OpenModbus/OM-64DO/kicad/OM-64DO.kicad_sch

## KiCad design kicad/OM-64DO.kicad_sch (2026-03-12)

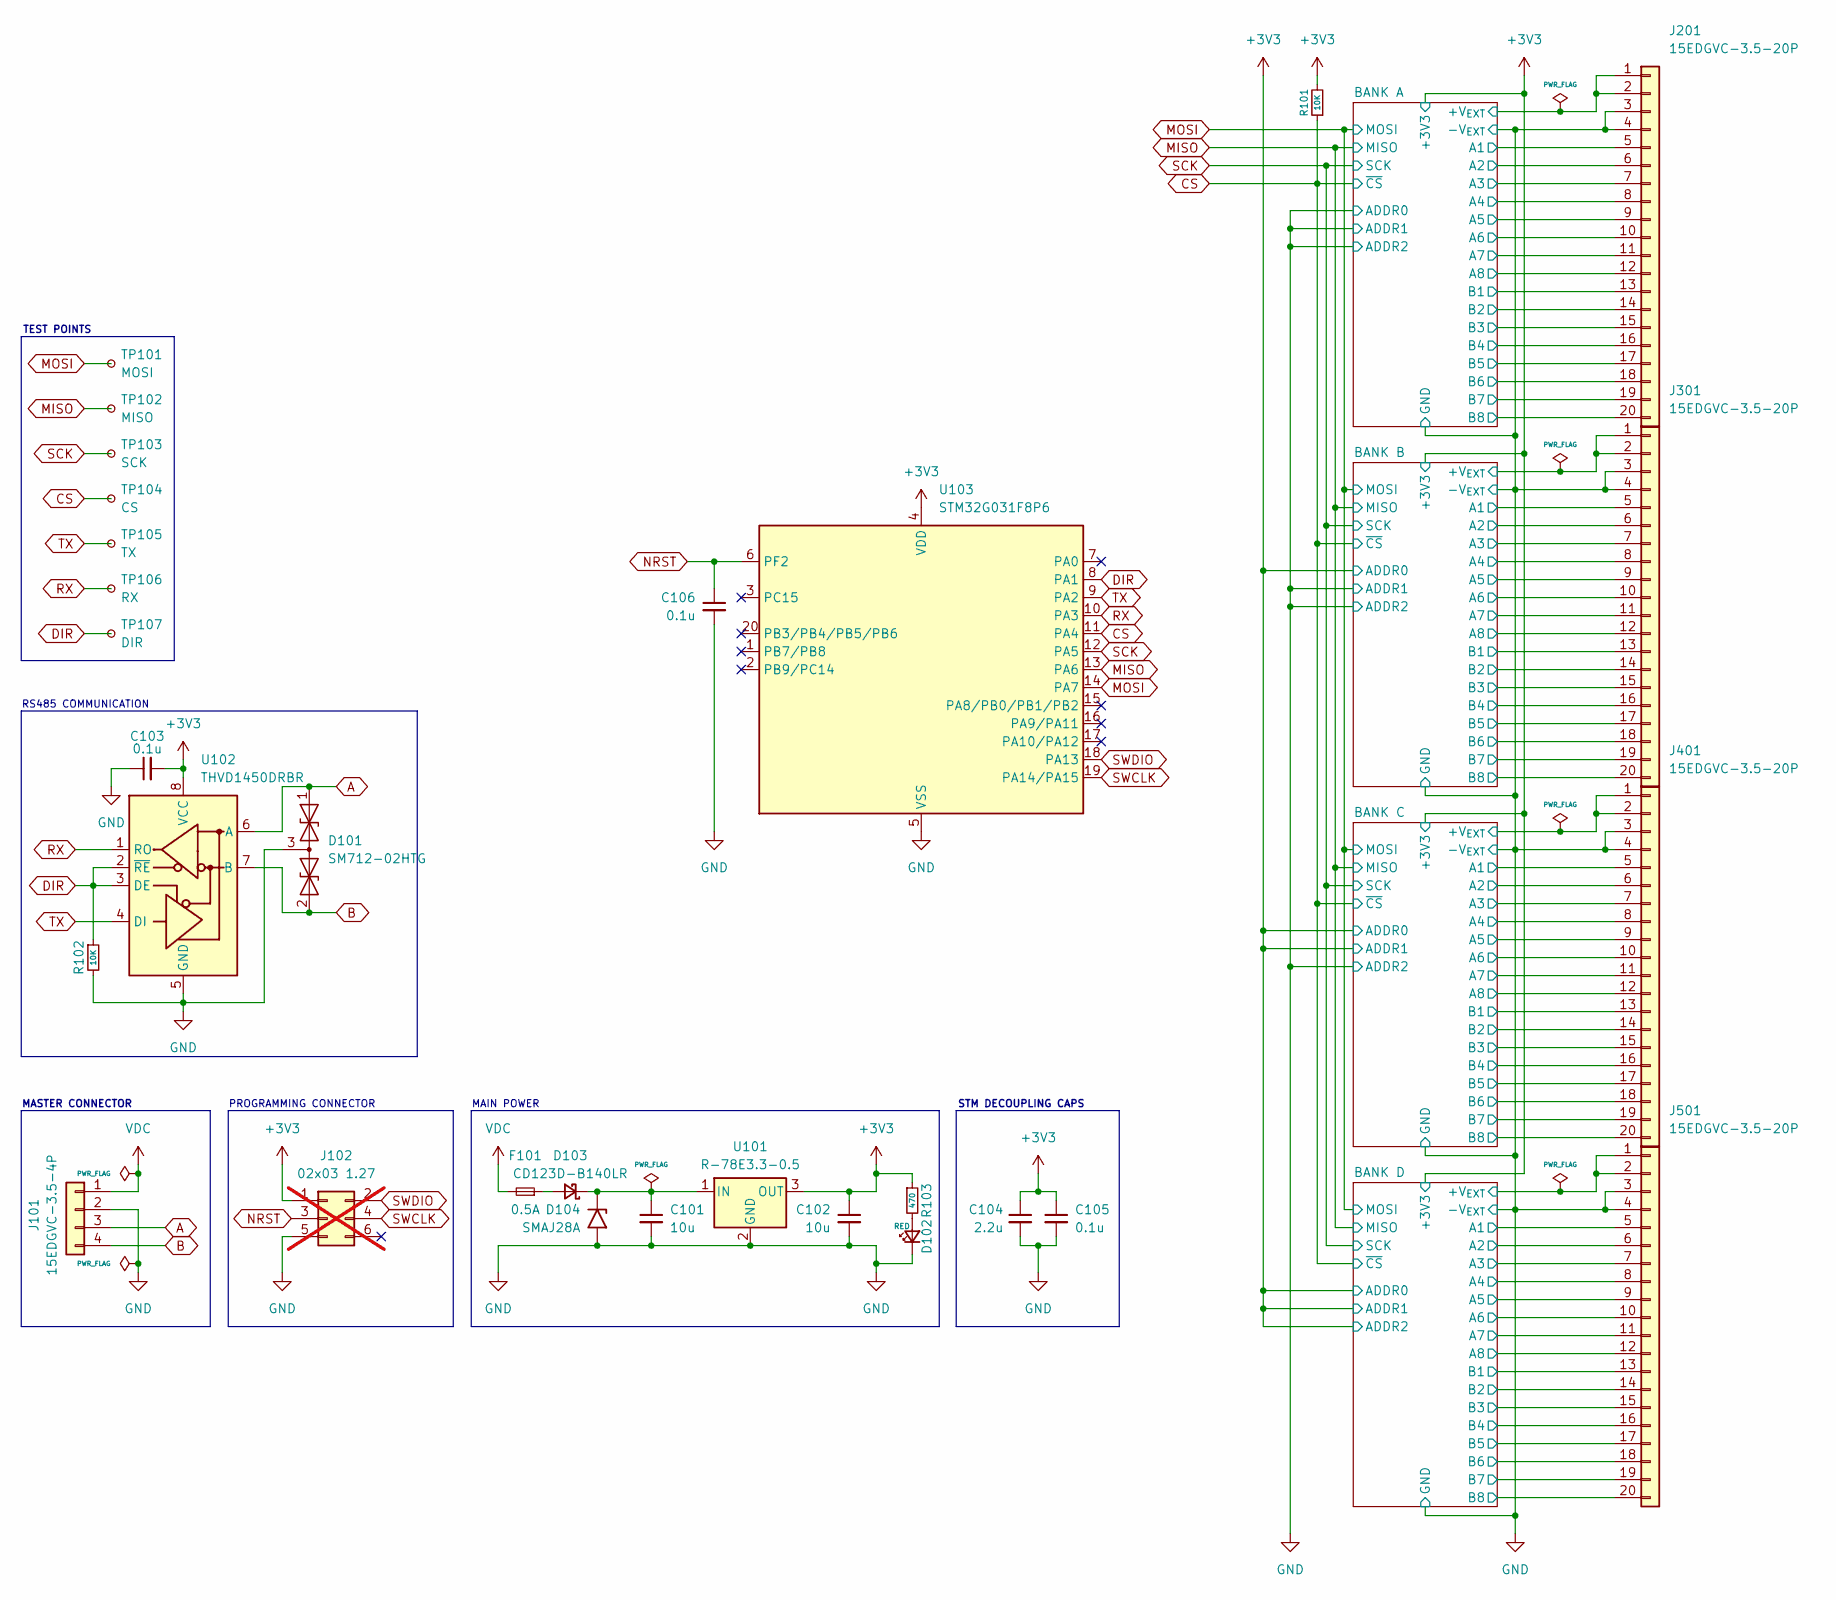
[picture p15: schematic OM-64DO.kicad_sch]

Parts:
C101, C102: 10u; C_1206_3216Metric; Part Number GRT31CR61H106KE01L; LCSC# C417124
C103, C105, C106: 0.1u; C_0603_1608Metric; Part Number GCJ188R71H104KA12D; LCSC# C161115
C104: 2.2u; C_0603_1608Metric; Part Number GRT188R61H225KE13D; LCSC# C668370
D101: SM712-02HTG; SOT-23; Part Number SM712-02HTG; LCSC# C172881
D102: RED; LED_0603_1608Metric; Part Number LTST-C190EKT; LCSC# C364560
D103: CD123D-B140LR; D_SOD-123; Part Number CD123D-B140LR; LCSC# C6877135
D104: SMAJ28A; D_SMA; Part Number SMAJ28A; LCSC# C148227
F101: 0.5A; Fuse_1206_3216Metric; Part Number 0466.500NR; LCSC# C151133
J101: 15EDGVC-3.5-4P; TerminalBlock_DEGSON_15EDGVC-3.5-4P_No_SilkScreen; Part Number 10030000681; LCSC# C22380434
J102: 02x03 1.27; PinHeader_2x03_P1.27mm_Vertical; not fitted
J201, J301, J401, J501: 15EDGVC-3.5-20P; TerminalBlock_DEGSON_15EDGVC-3.5-20P_No_SilkScreen; Part Number 10030000695; LCSC# C5188336
R101, R102: 10K; R_0603_1608Metric; Part Number ERJ-H3EF1002V; LCSC# C4297913
R103: 470; R_0603_1608Metric; Part Number ERJ-UP3J471V; LCSC# C491199
TP101: MOSI; TestPoint_Pad_D1.0mm
TP102: MISO; TestPoint_Pad_D1.0mm
TP103: SCK; TestPoint_Pad_D1.0mm
TP104: CS; TestPoint_Pad_D1.0mm
TP105: TX; TestPoint_Pad_D1.0mm
TP106: RX; TestPoint_Pad_D1.0mm
TP107: DIR; TestPoint_Pad_D1.0mm
U101: R-78E3.3-0.5; Converter_DCDC_RECOM_R-78E-0.5_THT; Part Number R-78E3.3-0.5; LCSC# C18212316
U102: THVD1450DRBR; VSON-8-1EP_3x3mm_P0.65mm_EP1.6x2.4mm; Part Number THVD1450DRBR; LCSC# C1850226
U103: STM32G031F8P6; TSSOP-20_4.4x6.5mm_P0.65mm; Part Number STM32G031F8P6; LCSC# C529334

Connections:
+3V3: C102.1, C103.2, C104.1, C105.1, J102.1, R101.2, R103.1, U101.3 (OUT), U102.8 (VCC), U103.4 (VDD)
+V_{EXT}: J201.1, J201.2, J301.1, J301.2, J401.1, J401.2, J501.1, J501.2
A: D101.1 (A1), J101.3, U102.6 (A)
A1: J201.5, J301.5, J401.5, J501.5
A2: J201.6, J301.6, J401.6, J501.6
A3: J201.7, J301.7, J401.7, J501.7
A4: J201.8, J301.8, J401.8, J501.8
A5: J201.9, J301.9, J401.9, J501.9
A6: J201.10, J301.10, J401.10, J501.10
A7: J201.11, J301.11, J401.11, J501.11
A8: J201.12, J301.12, J401.12, J501.12
B: D101.2 (A2), J101.4, U102.7 (B)
B1: J201.13, J301.13, J401.13, J501.13
B2: J201.14, J301.14, J401.14, J501.14
B3: J201.15, J301.15, J401.15, J501.15
B4: J201.16, J301.16, J401.16, J501.16
B5: J201.17, J301.17, J401.17, J501.17
B6: J201.18, J301.18, J401.18, J501.18
B7: J201.19, J301.19, J401.19, J501.19
B8: J201.20, J301.20, J401.20, J501.20
CS: R101.1, TP104.1, U103.11 (PA4)
DIR: R102.1, TP107.1, U102.2 (~RE), U102.3 (DE), U103.8 (PA1)
GND: C101.2, C102.2, C103.1, C104.2, C105.2, C106.2, D101.3 (common), D102.1 (K), D104.2 (A2), J101.2, J102.5, J201.3, J201.4, J301.3, J301.4, J401.3, J401.4, J501.3, J501.4, R102.2, U101.2 (GND), U102.5 (GND), U102.9 (GND), U103.5 (VSS)
MISO: TP102.1, U103.13 (PA6)
MOSI: TP101.1, U103.14 (PA7)
NRST: C106.1, J102.3, U103.6 (PF2)
unnamed: C101.1, D103.1 (K), D104.1 (A1), U101.1 (IN)
unnamed: D102.2 (A), R103.2
unnamed: D103.2 (A), F101.1
RX: TP106.1, U102.1 (RO), U103.10 (PA3)
SCK: TP103.1, U103.12 (PA5)
SWCLK: J102.4, U103.19 (PA14/PA15)
SWDIO: J102.2, U103.18 (PA13)
TX: TP105.1, U102.4 (DI), U103.9 (PA2)
VDC: F101.2, J101.1

Notes on the sheet:
STM DECOUPLING CAPS
MASTER CONNECTOR
RS485 COMMUNICATION
TEST POINTS
MAIN POWER
PROGRAMMING CONNECTOR
