OpenModbus/OM-64DO/kicad/logic_block.kicad_sch

## KiCad design kicad/logic_block.kicad_sch (2026-03-12)

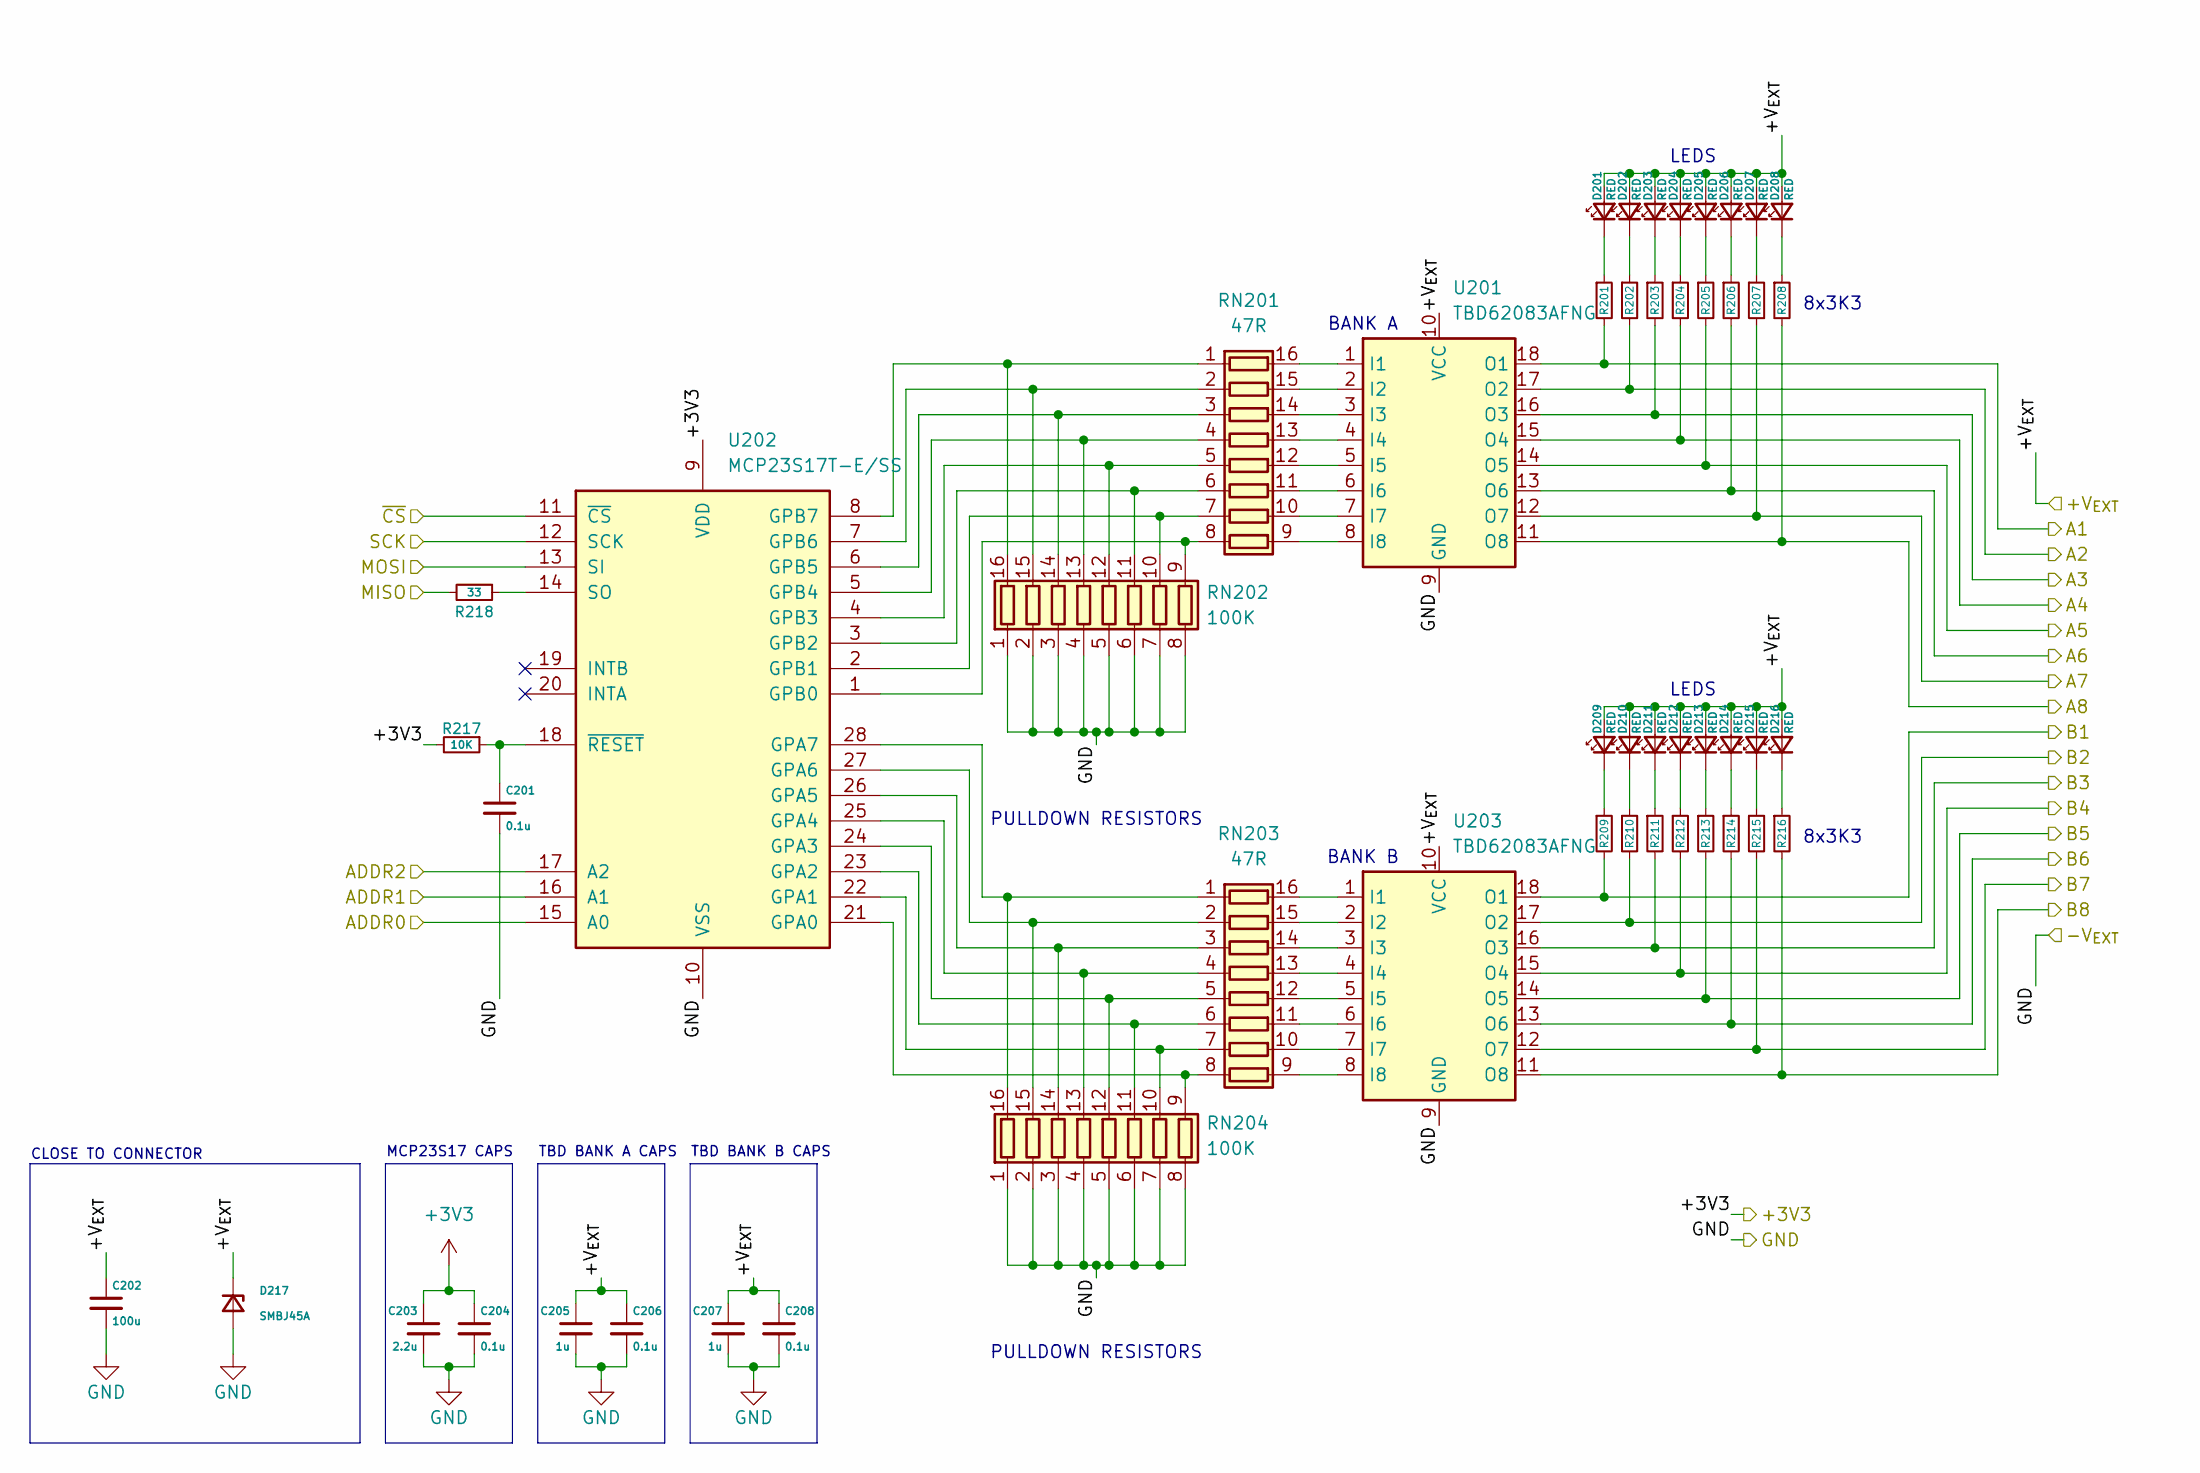
[picture p16: schematic logic_block.kicad_sch]

Parts:
C201, C204, C206, C208: 0.1u; C_0603_1608Metric; Part Number GCJ188R71H104KA12D; LCSC# C161115
C202: 100u; CP_Elec_8x10; Part Number UCM1J101MNL1GS; LCSC# C445456
C203: 2.2u; C_0603_1608Metric; Part Number GRT188R61H225KE13D; LCSC# C668370
C205, C207: 1u; C_0603_1608Metric; Part Number GRT188R61H105KE13D; LCSC# C126631
D201, D202, D203, D204, D205, D206, D207, D208, D209, D210, D211, D212, D213, D214, D215, D216: RED; LED_0603_1608Metric; Part Number LTST-C190EKT; LCSC# C364560
D217: SMBJ45A; D_SMB; Part Number SMBJ45A; LCSC# C720171
R201, R202, R203, R204, R205, R206, R207, R208, R209, R210, R211, R212, R213, R214, R215, R216: 3K3; R_0603_1608Metric; Part Number ERJ-UP3J332V; LCSC# C491202
R217: 10K; R_0603_1608Metric; Part Number ERJ-H3EF1002V; LCSC# C4297913
R218: 33; R_0603_1608Metric; Part Number ERJ-H3EF33R0V; LCSC# C4313361
RN201, RN203: 47R; R_Array_Convex_8x0602_EXB2HV; Part Number EXB-2HV470JV; LCSC# C713462
RN202, RN204: 100K; R_Array_Convex_8x0602_EXB2HV; Part Number EXB-2HV104JV; LCSC# C713455
U201, U203: TBD62083AFNG; SSOP-18_4.4x6.5mm_P0.65mm; Part Number TBD62083AFNG,EL; LCSC# C163229
U202: MCP23S17T-E/SS; SSOP-28_5.3x10.2mm_P0.65mm; Part Number MCP23S17T-E/SS; LCSC# C128577

Connections:
+3V3: C203.1, C204.1, R217.2, U202.9 (VDD)
+V_{EXT}: C202.1, C205.1, C206.1, C207.1, C208.1, D201.2 (A), D202.2 (A), D203.2 (A), D204.2 (A), D205.2 (A), D206.2 (A), D207.2 (A), D208.2 (A), D209.2 (A), D210.2 (A), D211.2 (A), D212.2 (A), D213.2 (A), D214.2 (A), D215.2 (A), D216.2 (A), D217.1 (K), U201.10 (VCC), U203.10 (VCC)
-V_{EXT}: C201.2, RN202.1 (R1.1), RN202.2 (R2.1), RN202.3 (R3.1), RN202.4 (R4.1), RN202.5 (R5.1), RN202.6 (R6.1), RN202.7 (R7.1), RN202.8 (R8.1), RN204.1 (R1.1), RN204.2 (R2.1), RN204.3 (R3.1), RN204.4 (R4.1), RN204.5 (R5.1), RN204.6 (R6.1), RN204.7 (R7.1), RN204.8 (R8.1), U201.9 (GND), U202.10 (VSS), U203.9 (GND)
A1: R201.2, U201.18 (O1)
A2: R202.2, U201.17 (O2)
A3: R203.2, U201.16 (O3)
A4: R204.2, U201.15 (O4)
A5: R205.2, U201.14 (O5)
A6: R206.2, U201.13 (O6)
A7: R207.2, U201.12 (O7)
A8: R208.2, U201.11 (O8)
ADDR0: U202.15 (A0)
ADDR1: U202.16 (A1)
ADDR2: U202.17 (A2)
B1: R209.2, U203.18 (O1)
B2: R210.2, U203.17 (O2)
B3: R211.2, U203.16 (O3)
B4: R212.2, U203.15 (O4)
B5: R213.2, U203.14 (O5)
B6: R214.2, U203.13 (O6)
B7: R215.2, U203.12 (O7)
B8: R216.2, U203.11 (O8)
GND: C202.2, C203.2, C204.2, C205.2, C206.2, C207.2, C208.2, D217.2 (A)
MISO: R218.2
MOSI: U202.13 (SI)
unnamed: C201.1, R217.1, U202.18 (~RESET)
unnamed: D201.1 (K), R201.1
unnamed: D202.1 (K), R202.1
unnamed: D203.1 (K), R203.1
unnamed: D204.1 (K), R204.1
unnamed: D205.1 (K), R205.1
unnamed: D206.1 (K), R206.1
unnamed: D207.1 (K), R207.1
unnamed: D208.1 (K), R208.1
unnamed: D209.1 (K), R209.1
unnamed: D210.1 (K), R210.1
unnamed: D211.1 (K), R211.1
unnamed: D212.1 (K), R212.1
unnamed: D213.1 (K), R213.1
unnamed: D214.1 (K), R214.1
unnamed: D215.1 (K), R215.1
unnamed: D216.1 (K), R216.1
unnamed: R218.1, U202.14 (SO)
unnamed: RN201.1 (R1.1), RN202.16 (R1.2), U202.8 (GPB7)
unnamed: RN201.2 (R2.1), RN202.15 (R2.2), U202.7 (GPB6)
unnamed: RN201.3 (R3.1), RN202.14 (R3.2), U202.6 (GPB5)
unnamed: RN201.4 (R4.1), RN202.13 (R4.2), U202.5 (GPB4)
unnamed: RN201.5 (R5.1), RN202.12 (R5.2), U202.4 (GPB3)
unnamed: RN201.6 (R6.1), RN202.11 (R6.2), U202.3 (GPB2)
unnamed: RN201.7 (R7.1), RN202.10 (R7.2), U202.2 (GPB1)
unnamed: RN201.8 (R8.1), RN202.9 (R8.2), U202.1 (GPB0)
unnamed: RN201.9 (R8.2), U201.8 (I8)
unnamed: RN201.10 (R7.2), U201.7 (I7)
unnamed: RN201.11 (R6.2), U201.6 (I6)
unnamed: RN201.12 (R5.2), U201.5 (I5)
unnamed: RN201.13 (R4.2), U201.4 (I4)
unnamed: RN201.14 (R3.2), U201.3 (I3)
unnamed: RN201.15 (R2.2), U201.2 (I2)
unnamed: RN201.16 (R1.2), U201.1 (I1)
unnamed: RN203.1 (R1.1), RN204.16 (R1.2), U202.28 (GPA7)
unnamed: RN203.2 (R2.1), RN204.15 (R2.2), U202.27 (GPA6)
unnamed: RN203.3 (R3.1), RN204.14 (R3.2), U202.26 (GPA5)
unnamed: RN203.4 (R4.1), RN204.13 (R4.2), U202.25 (GPA4)
unnamed: RN203.5 (R5.1), RN204.12 (R5.2), U202.24 (GPA3)
unnamed: RN203.6 (R6.1), RN204.11 (R6.2), U202.23 (GPA2)
unnamed: RN203.7 (R7.1), RN204.10 (R7.2), U202.22 (GPA1)
unnamed: RN203.8 (R8.1), RN204.9 (R8.2), U202.21 (GPA0)
unnamed: RN203.9 (R8.2), U203.8 (I8)
unnamed: RN203.10 (R7.2), U203.7 (I7)
unnamed: RN203.11 (R6.2), U203.6 (I6)
unnamed: RN203.12 (R5.2), U203.5 (I5)
unnamed: RN203.13 (R4.2), U203.4 (I4)
unnamed: RN203.14 (R3.2), U203.3 (I3)
unnamed: RN203.15 (R2.2), U203.2 (I2)
unnamed: RN203.16 (R1.2), U203.1 (I1)
SCK: U202.12 (SCK)
~CS: U202.11 (~CS)

Notes on the sheet:
MCP23S17 CAPS
8x3K3
BANK B
PULLDOWN RESISTORS
LEDS
BANK A
CLOSE TO CONNECTOR
TBD BANK B CAPS
TBD BANK A CAPS
